proboterror/zx-rgbi-to-vga-hdmi_gotek-osd/ZX_RGBI_TO_VGA_HDMI/gotek_i2c_osd.h

#pragma once

struct display
{
    int rows, cols, on;
    uint8_t text[4][40];
};

extern struct display i2c_display;

void osd_process();
void setup_i2c_slave();

#define OSD_BUTTON_LEFT 1
#define OSD_BUTTON_RIGHT 2
#define OSD_BUTTON_SELECT 4

void set_osd_buttons(uint8_t buttons);
