proboterror/zx-rgbi-to-vga-hdmi_gotek-osd/ZX_RGBI_TO_VGA_HDMI/pio_programs.h

#ifndef PIO_PROGRAMS_H
#define PIO_PROGRAMS_H

#include "hardware/pio.h"

extern const uint16_t nop_opcode;

extern const struct pio_program pio_program_capture_0;
extern uint16_t pio_program_capture_0_instructions[];

extern const uint16_t set_opcode;

extern const struct pio_program pio_program_capture_1;
extern uint16_t pio_program_capture_1_instructions[];

extern const struct pio_program pio_program_vga;
extern uint16_t pio_program_vga_instructions[];

extern const struct pio_program pio_program_dvi;
extern uint16_t pio_program_dvi_instructions[];

#endif
