proboterror/zx-rgbi-to-vga-hdmi_gotek-osd/ZX_RGBI_TO_VGA_HDMI/v_buf.h

#ifndef VBUF_H
#define VBUF_H

void *get_v_buf_out();
void *get_v_buf_in();
void set_v_buf_buffering_mode(bool);

void draw_welcome_screen(video_mode_t video_mode);
void draw_welcome_screen_h(video_mode_t video_mode);

#endif
